azizcanhamas/iot-web-based-electronic-attendance-system/codes/arduino/rfid_arduino/RFID_rc522_00.jpg

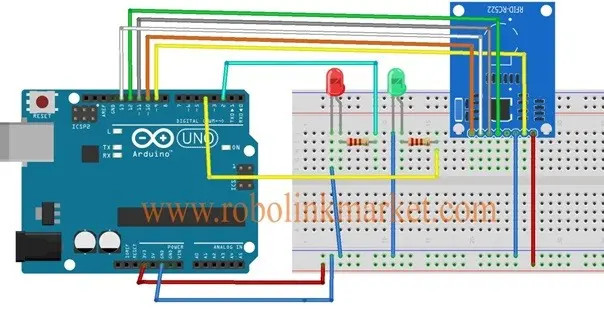
codes/arduino/rfid_arduino/RFID_rc522_00.jpg
