azizcanhamas/iot-web-based-electronic-attendance-system/codes/arduino/u8glib_oled/arduino_oled_ekran_baglanti_semasi.jpg

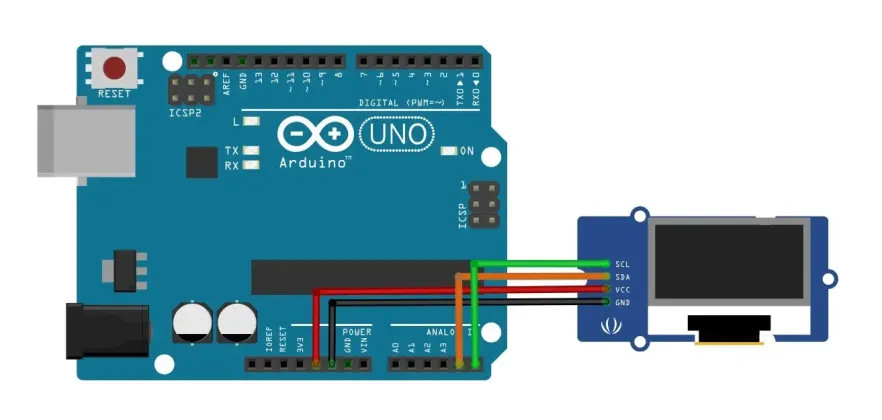
codes/arduino/u8glib_oled/arduino_oled_ekran_baglanti_semasi.jpg
