azizcanhamas/iot-web-based-electronic-attendance-system/codes/nodemcu/rfid/nodemcu_rfid_calisiyor.jpg

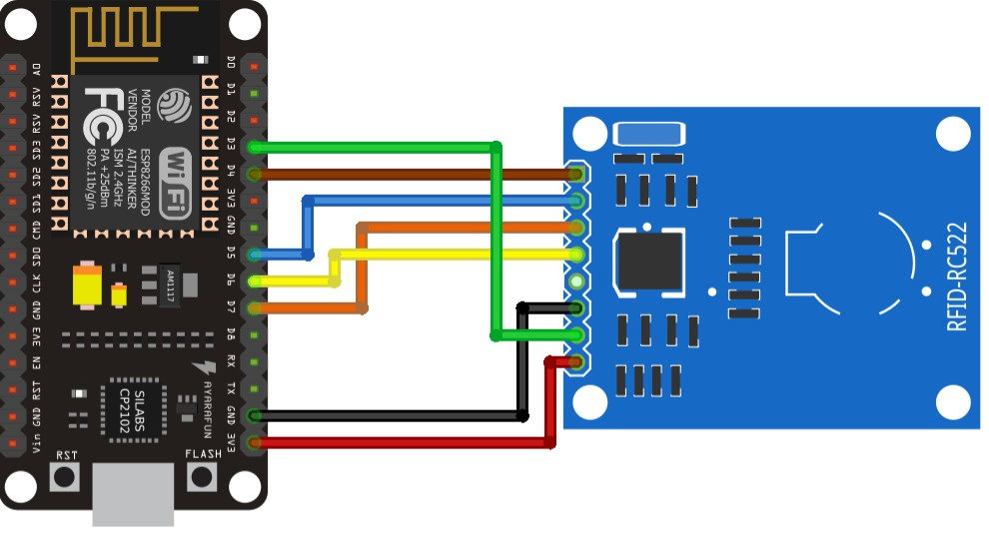
codes/nodemcu/rfid/nodemcu_rfid_calisiyor.jpg
