azizcanhamas/iot-web-based-electronic-attendance-system/diagrams/mechanical_draws/project-box-pr-120.jpg

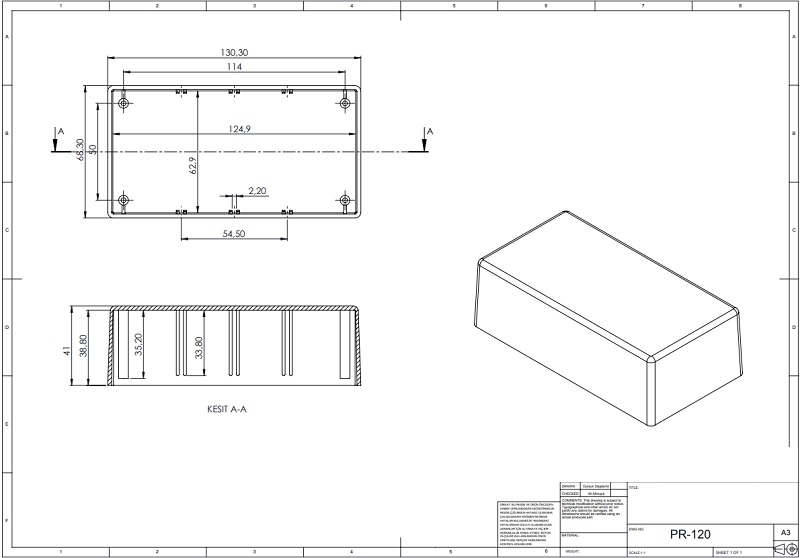
diagrams/mechanical_draws/project-box-pr-120.jpg
