azizcanhamas/iot-web-based-electronic-attendance-system/diagrams/nodemcu_pinout/nodemcu-pinout-v2.jpg

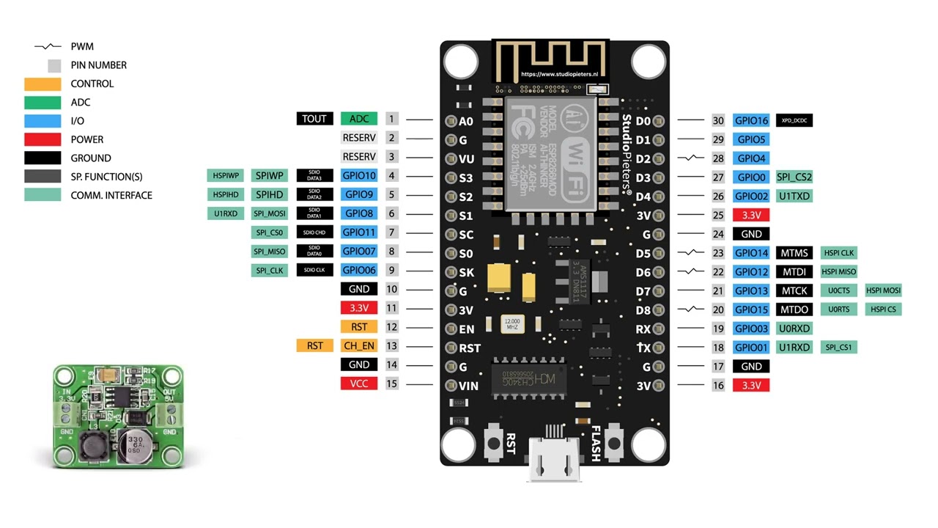
diagrams/nodemcu_pinout/nodemcu-pinout-v2.jpg
