azizcanhamas/iot-web-based-electronic-attendance-system/diagrams/nodemcu_pinout/nodemcu-pinout.jpg

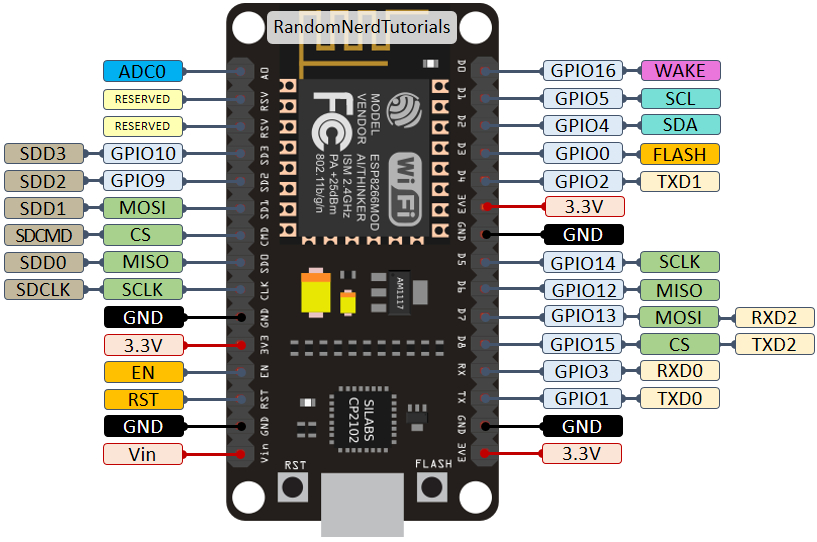
diagrams/nodemcu_pinout/nodemcu-pinout.jpg
