azizcanhamas/iot-web-based-electronic-attendance-system/web/project/web/src/main/java/com/bitirme/web/Controller/APIController/DeviceAPI.java

package com.bitirme.web.Controller.APIController;


import com.bitirme.web.Entity.*;
import com.bitirme.web.Repository.*;
import org.springframework.beans.factory.annotation.Autowired;
import org.springframework.security.crypto.bcrypt.BCryptPasswordEncoder;
import org.springframework.web.bind.annotation.GetMapping;
import org.springframework.web.bind.annotation.RequestParam;
import org.springframework.web.bind.annotation.RestController;

import java.text.ParseException;
import java.time.LocalDate;
import java.time.LocalDateTime;
import java.time.format.DateTimeFormatter;
import java.util.*;

@RestController
public class DeviceAPI {

    @Autowired
    private CihazRepository cihazRepo;

    @Autowired
    private CihazIstekleriRepository cihazIstekleriRepo;

    @Autowired
    private DersRepository dersRepo;

    @Autowired
    private OgrenciRepository ogrenciRepo;

    //Kart okutuldugu zaman Cihaz tarafindan bu fonksiyon tetiklenecektir.
    @GetMapping("/api/varYaz")
    public Map<String,String> varYaz(CihazIstekleri cihazIstek) throws ParseException {

        System.out.println(cihazIstek.getCihazToken());
        System.out.println(cihazIstek.getRfidKodu());

        List<Cihaz> c=cihazRepo.findAll();
        HashMap<String, String> map = new HashMap<>();
        BCryptPasswordEncoder encoder=new BCryptPasswordEncoder();
        for(Cihaz tmp:c){
            // Cihazin tabloda kayitli olup olmadiginin kontrolu
            // Token tabloda encrypted olarak tutulmaktadir.
            if(encoder.matches(cihazIstek.getCihazToken(),
                    tmp.getCihazToken())){
                DateTimeFormatter dtf = DateTimeFormatter.ofPattern("yyyy/MM/dd HH:mm:ss");
                LocalDateTime now = LocalDateTime.now();
                cihazIstek.setIstekZamani(now.format(dtf));
                //cihazin hangi sinifta calistigi biliniyor.
                cihazIstek.setSinifKodu(tmp.getSinifKodu());
                cihazIstek.setCihazToken(tmp.getCihazToken());

                //Ilgili sinifta islenen dersin kodunu bul.
                String gunNumber= String.valueOf(LocalDate.now().getDayOfWeek().getValue()-1);
                String saat= String.valueOf(Calendar.getInstance().get(Calendar.HOUR_OF_DAY));
                Ders d=dersRepo.getCurrentLesson(tmp.getSinifKodu(),gunNumber,saat+":00");
                System.out.println("1 : "+tmp.getSinifKodu());
                System.out.println("2 : "+gunNumber);
                System.out.println("3 : "+saat);
                if(d==null){
                    map.put("message","Bu sinifta ders islenmiyor!");
                    return map;
                }
                else{
                    Ogrenci ogr=ogrenciRepo.getOgrenciByRfidKodu(cihazIstek.getRfidKodu());
                    if(ogr==null){
                        map.put("message","Derse kayitli degilsiniz!");
                    }
                    else {
                        cihazIstek.setDersKodu(d.getDersKodu());
                        cihazIstek.setPersonelNo(d.getPersonelNo());

                        cihazIstekleriRepo.save(cihazIstek);

                        map.put("message", "Yoklama alındı!");
                    }
                    return map;
                }
            }
        }
        map.put("message","Tanimsiz cihaz!");
        return map;
    }

    //Cihaz bulundugu sinifta islenen dersi gosterebilmek icin bu fonksiyonu tetikleyecektir.
    @GetMapping("/api/getLesson")
    public Map<String,String> getLesson(@RequestParam("cihazToken") String cihazToken){
        List<Cihaz> c=cihazRepo.findAll();
        BCryptPasswordEncoder encoder=new BCryptPasswordEncoder();
        HashMap<String,String>map=new HashMap<>();
        for(Cihaz tmp:c){
            if(encoder.matches(cihazToken,tmp.getCihazToken())){
                map.put("sinif",tmp.getSinifKodu());

                String gunNumber= String.valueOf(LocalDate.now().getDayOfWeek().getValue());
                String saat= String.valueOf(Calendar.getInstance().get(Calendar.HOUR_OF_DAY));

                System.out.println("=========== GUN   : "+gunNumber);
                System.out.println("=========== SAAT  : "+saat);
                System.out.println("=========== SINIF : "+tmp.getSinifKodu());

                Ders d=dersRepo.getCurrentLesson(tmp.getSinifKodu(),gunNumber,saat);
                map.put("dersAdi",d.getDersAdi());
                return map;
            }
        }
        map.put("message","Cihaz kayitli degil!");
        return map;
    }
}
