azizcanhamas/iot-web-based-electronic-attendance-system/web/project/web/src/main/java/com/bitirme/web/Security/WebSecurityConfig.java

package com.bitirme.web.Security;

import com.bitirme.web.CustomUserDetails.CustomUserDetailsService;
import com.bitirme.web.Security.LoginSuccessHandler;
import org.springframework.beans.factory.annotation.Autowired;
import org.springframework.context.annotation.Bean;
import org.springframework.context.annotation.Configuration;
import org.springframework.http.HttpMethod;
import org.springframework.security.authentication.dao.DaoAuthenticationProvider;
import org.springframework.security.config.annotation.authentication.builders.AuthenticationManagerBuilder;
import org.springframework.security.config.annotation.web.builders.HttpSecurity;
import org.springframework.security.config.annotation.web.configuration.EnableWebSecurity;
import org.springframework.security.config.annotation.web.configuration.WebSecurityConfigurerAdapter;
import org.springframework.security.core.userdetails.UserDetailsService;
import org.springframework.security.crypto.bcrypt.BCryptPasswordEncoder;

@Configuration
@EnableWebSecurity
public class WebSecurityConfig extends WebSecurityConfigurerAdapter {
    @Autowired private LoginSuccessHandler successHandler;

    @Bean
    public UserDetailsService userDetailsService() {
        return new CustomUserDetailsService();
    }

    @Bean
    public BCryptPasswordEncoder passwordEncoder() {
        return new BCryptPasswordEncoder();
    }

    @Bean
    public DaoAuthenticationProvider authenticationProvider() {
        DaoAuthenticationProvider authProvider = new DaoAuthenticationProvider();
        authProvider.setUserDetailsService(userDetailsService());
        authProvider.setPasswordEncoder(passwordEncoder());

        return authProvider;
    }

    @Override
    protected void configure(AuthenticationManagerBuilder auth) throws Exception {
        auth.authenticationProvider(authenticationProvider());
    }

    // ================ WITHOUT API AUTHENTICATION ==================
//    @Override
//    protected void configure(HttpSecurity http) throws Exception {
//        http.authorizeRequests()
//                .antMatchers("/","/assets/**")
//                .permitAll()
//
//                .antMatchers("/ogrenci-panel")
//                .hasAuthority("USER")
//
//                .antMatchers("/home")
//                .hasAuthority("ADMIN")
//
//                .anyRequest()
//                .authenticated()
//                .and()
//                    .formLogin()
//                    .loginPage("/login")
//                    .usernameParameter("username")
//                    .passwordParameter("password")
//                    .loginProcessingUrl("/process-login")
////                    .defaultSuccessUrl("/home") //HTTP 403'e sebep oluyor.
//                    .successHandler(successHandler)
//                    .permitAll()
//                .and()
//                    .logout().logoutSuccessUrl("/").permitAll()
//                .and()
//                    .csrf()
//                    .disable();
//    }


    @Override
    protected void configure(HttpSecurity http) throws Exception {
        http
                .httpBasic()  // ===== API CONFIGURATION
                    .and()
                        .authorizeRequests()
                        .antMatchers(HttpMethod.GET,"/api").hasAuthority("ADMIN")
                    .and()
                        .csrf().disable()
                .authorizeRequests()// ===== VIEW CONFIGURATION
                    .antMatchers("/","/assets/**")
                    .permitAll()
                    .antMatchers("/ogrenci-panel")
                    .hasAuthority("USER")
                    .antMatchers("/home")
                    .hasAuthority("ADMIN")
                    .anyRequest()
                    .authenticated()
                .and()
                    .formLogin()
                        .loginPage("/login")
                        .usernameParameter("username")
                        .passwordParameter("password")
                        .loginProcessingUrl("/process-login")
//                      .defaultSuccessUrl("/home") //HTTP 403'e sebep oluyor.
                        .successHandler(successHandler)
                        .permitAll()
                .and()
                    .logout()
                    .logoutSuccessUrl("/")
                    .permitAll();

    }
}
